zchap40/electron-ostc/Renders/ostc_v2/Images/ostc_v2_cmp.jpg

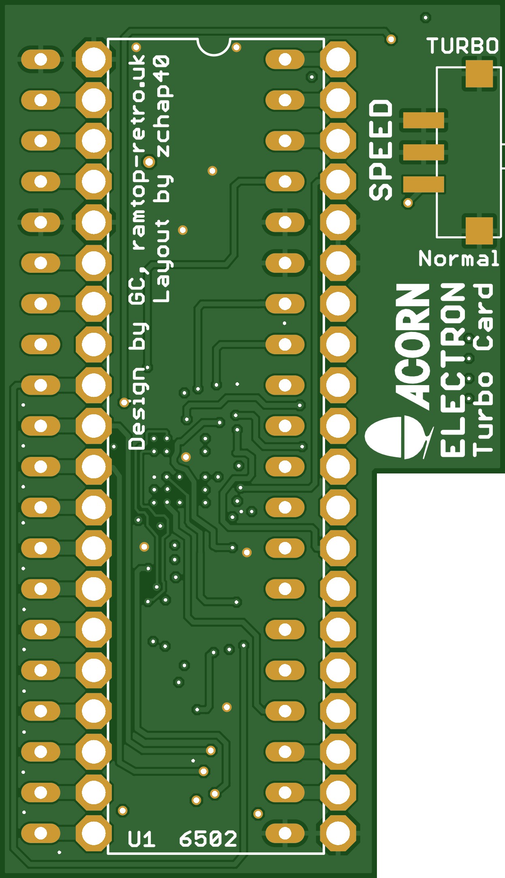
Renders/ostc_v2/Images/ostc_v2_cmp.jpg
